wlyoung/Lima-Shelter-20/dxf/three quarter/Lima Sleepers cut 2.dxf

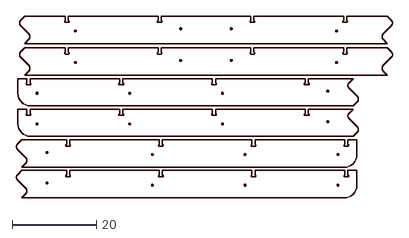
[picture p21: CAD file, 2017-05-24]
dxf/three quarter/Lima Sleepers cut 2.dxf
89.4 x 43.1
