wlyoung/Lima-Shelter-20/dxf/three quarter/Lima Endwall door option parts cut 1.dxf

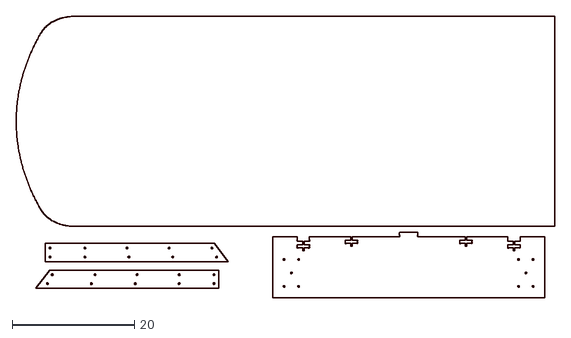
[picture p22: CAD file, 2017-05-24]
dxf/three quarter/Lima Endwall door option parts cut 1.dxf
88.2 x 46.1
