wlyoung/Lima-Shelter-20/dxf/three quarter/Lima Endwall 2 headers cut 1.dxf

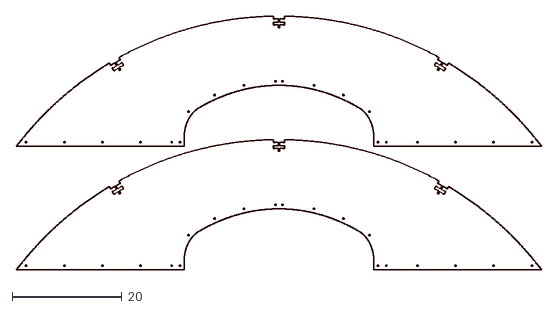
[picture p23: CAD file, 2017-05-10]
dxf/three quarter/Lima Endwall 2 headers cut 1.dxf
95.5 x 46.1
